ergohaven/hpd/step/modules/trackball-body.stp

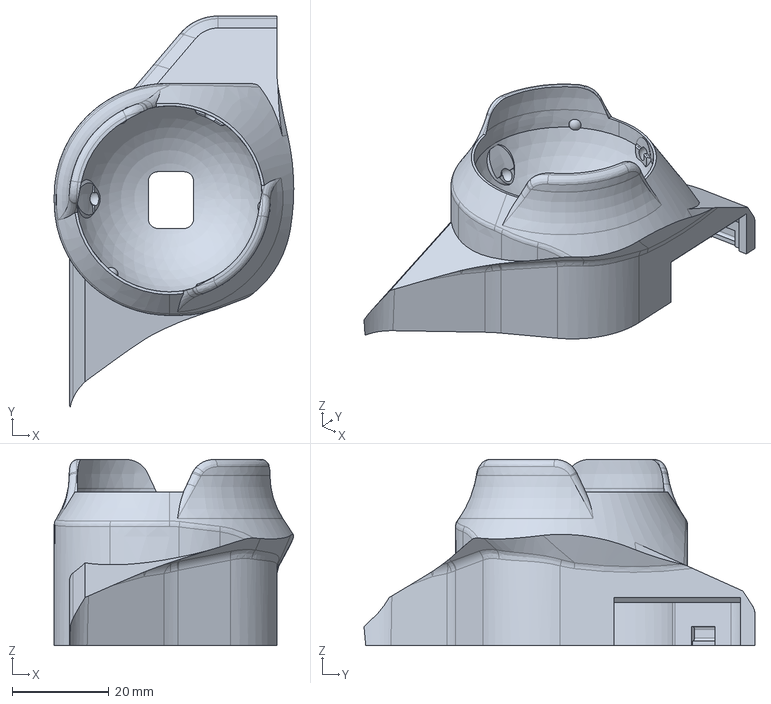
[picture p24: CAD file, 2026-04-23]
step/modules/trackball-body.stp
49.6 x 81.0 x 38.6 mm
