ergohaven/hpd/step/modules/trackball-bot.stp

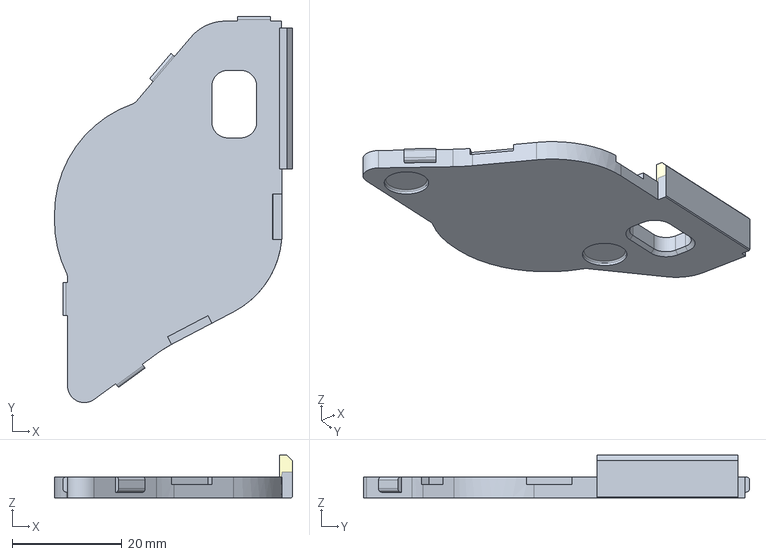
[picture p25: CAD file, 2026-04-23]
step/modules/trackball-bot.stp
43.3 x 70.3 x 7.78 mm
