ergohaven/hpd/step/modules/touchpad-bot.stp

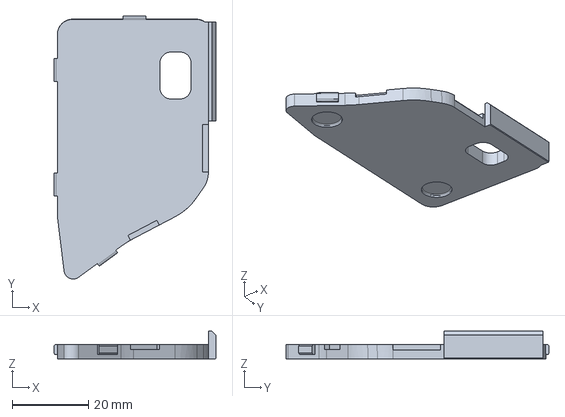
[picture p26: CAD file, 2026-04-23]
step/modules/touchpad-bot.stp
42.4 x 68.9 x 7.28 mm
